Silveriomrs/micropicodrive/Firmware 2.0 (By Popopo)/src/View.h

/**
* This module manage the View/GUI between RBPi Pico and the oLED Screen of 0.49" and LEDs Behavior.
* @Author: Original work from Dr. Gusman project.
* @Author: Silverio MRS (Popopo)
* @Version: 1.0.2
*/

#ifndef _VIEW_
#define _VIEW_
// #include "pff/pff.h"  //TODO: Delete me if all is fine after a time of testing.
#include <string.h>
#include <stdio.h>
#include "ssd1306/ssd1306.h"

//LEDs Pins output
#define LED_PWR 25		/** Power LED RPB Pico */
#define LED_SELECT 9	/** LED unit selected */
#define LED_READ 11		/** LED unit in reading state */
#define LED_WRITE 10	/** LED unit in writing state */
//Screen and SDCart pins.
#define I2C_PORT i2c0
#define I2C_SDA 20
#define I2C_SCL 21
//Functions for managing the LED states
#define SET_LED_ON(LED) gpio_put(LED, true)		/** Set the indicated Led ON */
#define SET_LED_OFF(LED) gpio_put(LED, false)	/** Set the indicated Led OFF */

//Types of messages
typedef enum{
	WELCOME,
	SD_WAIT,
	//CART Messages mean to MDVs images, NOT TO SD cart.
	CART_RDY,
	CART_FORMAT_UNK,
	CART_ERR_LDING,
	CART_ERR_SAVING,
	CART_SAVING,
	CART_SAVED,
	//Folders messages
	FOLDER_ERR_OPEN,
	FOLDER_ERR_READ,
	FOLDER_EPTY,
	NO_MORE_FILES,
	//
	LDING_MDV,
	LDING_MDP,
	LDING_DEFAULT,
	ERR_CFG
} MSG_TYPE;

bool init_screen();
bool init_gui();
void setSCRM(const char* scrm);
void show_file_name(const char* fname, bool IN_FOLDER);
void showMSG(MSG_TYPE m);
void printMSG(const char* msg1, const char* msg2, const char* msg3, int time);
void printHorizontalScroll(const char*msg1, const char*msg2, int row, const int time);
void printVerticalScroll(const char*msg1, const char*msg2, const char* msg3, const int time);

#endif
